Pier1965/WebRadioEn/Docs/Bom/img/Condensatori.png

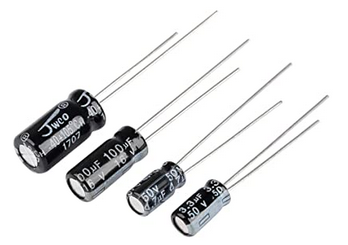
Docs/Bom/img/Condensatori.png
