Pier1965/WebRadioEn/Docs/Bom/img/IR.png

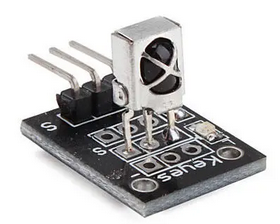
Docs/Bom/img/IR.png
