Pier1965/WebRadioEn/Docs/Bom/img/OLED-1603.png

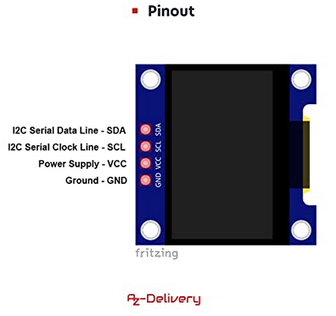
Docs/Bom/img/OLED-1603.png
