Pier1965/WebRadioEn/Docs/Bom/img/presa-55.png

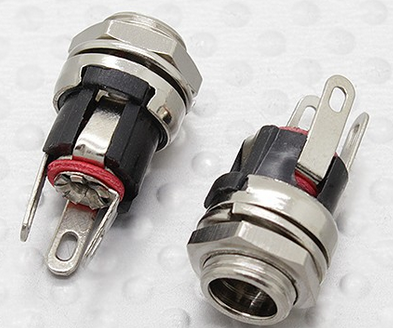
Docs/Bom/img/presa-55.png
