Pier1965/WebRadioEn/Docs/Bom/img/Pulsanti.png

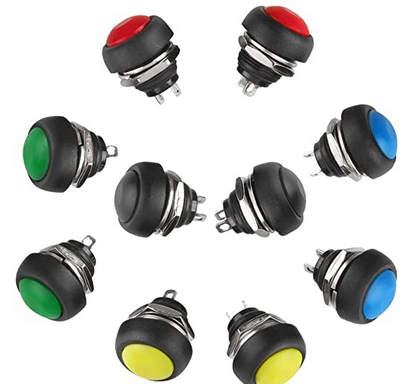
Docs/Bom/img/Pulsanti.png
