Pier1965/WebRadioEn/Docs/Bom/img/Radio.jpg

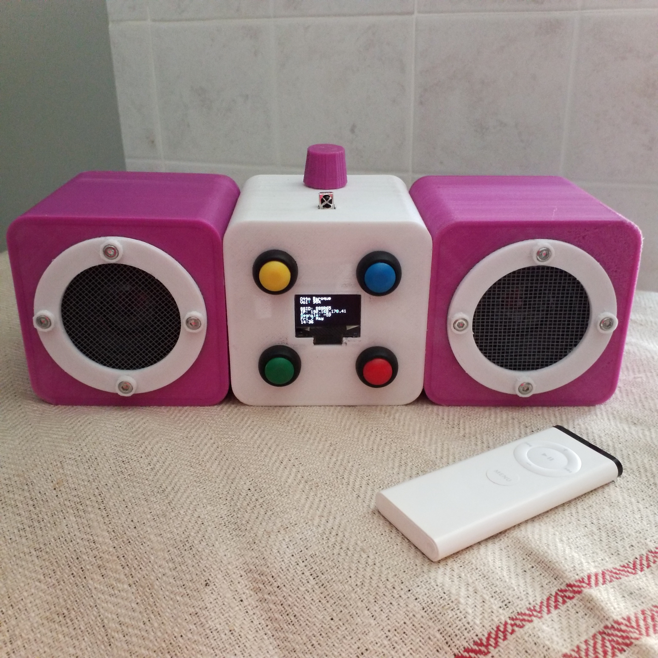
Docs/Bom/img/Radio.jpg
