Pier1965/WebRadioEn/Docs/Bom/img/Resistenza.png

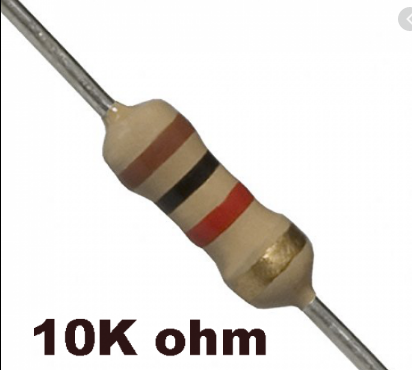
Docs/Bom/img/Resistenza.png
