Pier1965/WebRadioEn/Docs/Bom/img/speakers.png

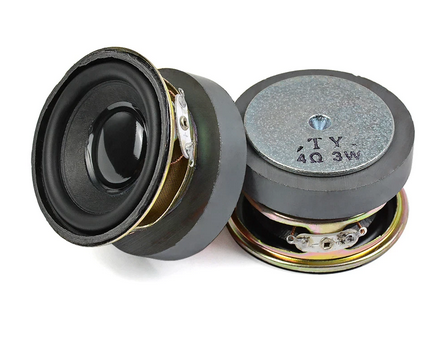
Docs/Bom/img/speakers.png
