Pier1965/WebRadioEn/Docs/Bom/img/VS1053.png

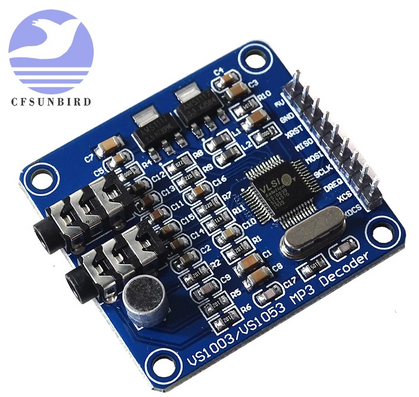
Docs/Bom/img/VS1053.png
